tgfuellner/TableTennisDisplay/Elektronic/tt-display.sch

## KiCad design Elektronic/tt-display.sch (2016-07-11)

Schematic: tt-display.sch

Parts:
1.22M: R
AFF1, AFF2: 7SEGMENTS
D1, D2: LED
SW1: Right
SW2: Left
U1, U2, U3, U4, U5, U6: TLC5916

Notes on the sheet:
Left Game klein
Left Point Einer
Left Point Zehner
Right Point Zehner
Right Point Einer
Right Game klein
Seperation
D0-D8 for Wemos D1 mini
Oled
Voricht: Wemos A0 ist Spannungsteiler
