tgfuellner/TableTennisDisplay/Software/rgbMatrix_I2c_32x64/Ubuntu_C16pt7b.h

const uint8_t Ubuntu_C16pt7bBitmaps[] PROGMEM = {
  0xEE, 0xEE, 0xEE, 0xEE, 0xEE, 0xEE, 0xE4, 0x00, 0x06, 0xFF, 0x60, 0xE7,
  0xE7, 0xE7, 0xE7, 0xE7, 0xE7, 0xE7, 0x42, 0x03, 0x0C, 0x03, 0x0C, 0x03,
  0x0C, 0x06, 0x18, 0x06, 0x18, 0x06, 0x18, 0xFF, 0xFF, 0xFF, 0xFF, 0x0C,
  0x30, 0x0C, 0x30, 0x0C, 0x30, 0x0C, 0x30, 0x0C, 0x30, 0xFF, 0xFF, 0xFF,
  0xFF, 0x18, 0x60, 0x18, 0x60, 0x18, 0x60, 0x30, 0xC0, 0x30, 0xC0, 0x30,
  0xC0, 0x1C, 0x0E, 0x07, 0x07, 0xC7, 0xF3, 0x8B, 0x81, 0xC0, 0xE0, 0x70,
  0x3C, 0x0F, 0x03, 0xC0, 0xF0, 0x3C, 0x0F, 0x03, 0x81, 0xC0, 0xE0, 0x7C,
  0x7F, 0xF9, 0xF8, 0x38, 0x1C, 0x0E, 0x07, 0x00, 0x38, 0x0E, 0x1F, 0x03,
  0x0E, 0xE1, 0xC3, 0x18, 0x60, 0xC6, 0x38, 0x31, 0x8E, 0x0C, 0x67, 0x03,
  0x19, 0xC0, 0xEE, 0x60, 0x1F, 0x38, 0x03, 0x8C, 0x70, 0x07, 0x3E, 0x01,
  0x9D, 0xC0, 0xE6, 0x30, 0x39, 0x8C, 0x1C, 0x63, 0x07, 0x18, 0xC1, 0x86,
  0x30, 0xE1, 0xDC, 0x30, 0x3E, 0x1C, 0x07, 0x00, 0x0F, 0x00, 0x7E, 0x03,
  0xFC, 0x0E, 0x70, 0x39, 0xC0, 0xE7, 0x03, 0x9C, 0x06, 0xE0, 0x1F, 0x00,
  0x38, 0x01, 0xE3, 0x8F, 0xCE, 0x73, 0xBB, 0x86, 0xEE, 0x1F, 0x38, 0x3C,
  0xE0, 0x63, 0xC3, 0xC7, 0xFF, 0x9F, 0xEE, 0x1F, 0x1C, 0xFF, 0xFF, 0xFA,
  0x04, 0x1C, 0x70, 0xE3, 0x87, 0x1C, 0x38, 0x70, 0xE3, 0x87, 0x0E, 0x1C,
  0x38, 0x70, 0xE1, 0xC3, 0x87, 0x07, 0x0E, 0x1C, 0x38, 0x38, 0x70, 0x70,
  0xE0, 0xE0, 0x80, 0x41, 0xC1, 0xC3, 0x83, 0x87, 0x07, 0x0E, 0x1C, 0x38,
  0x38, 0x70, 0xE1, 0xC3, 0x87, 0x0E, 0x1C, 0x38, 0x71, 0xC3, 0x87, 0x0E,
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
  {   895,   9,  21,  13,    3,  -20 },   // 0x46 'F'
  {   919,  12,  21,  16,    2,  -20 },   // 0x47 'G'
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

const GFXfont Ubuntu_C16pt7b PROGMEM = {
  (uint8_t  *)Ubuntu_C16pt7bBitmaps,
  (GFXglyph *)Ubuntu_C16pt7bGlyphs,
  0x20, 0x7E, 36 };

// Approx. 3084 bytes
